mizma/ergoSHIFT/hardware-rev1/acrylic-shell/acryl-design-ergoSHIFT-Acrylic-layer-03.dxf

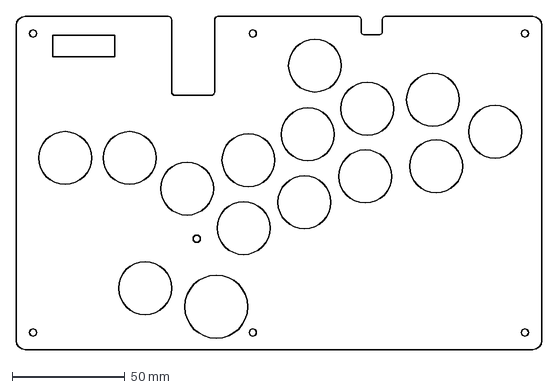
[picture p43: CAD file, 2023-12-16, an earlier design]
hardware-rev1/acrylic-shell/acryl-design-ergoSHIFT-Acrylic-layer-03.dxf
233.2 x 147.7 mm
