mizma/ergoSHIFT/ErgoSHIFT Layout/ErgoSHIFT_boardsize.pdf

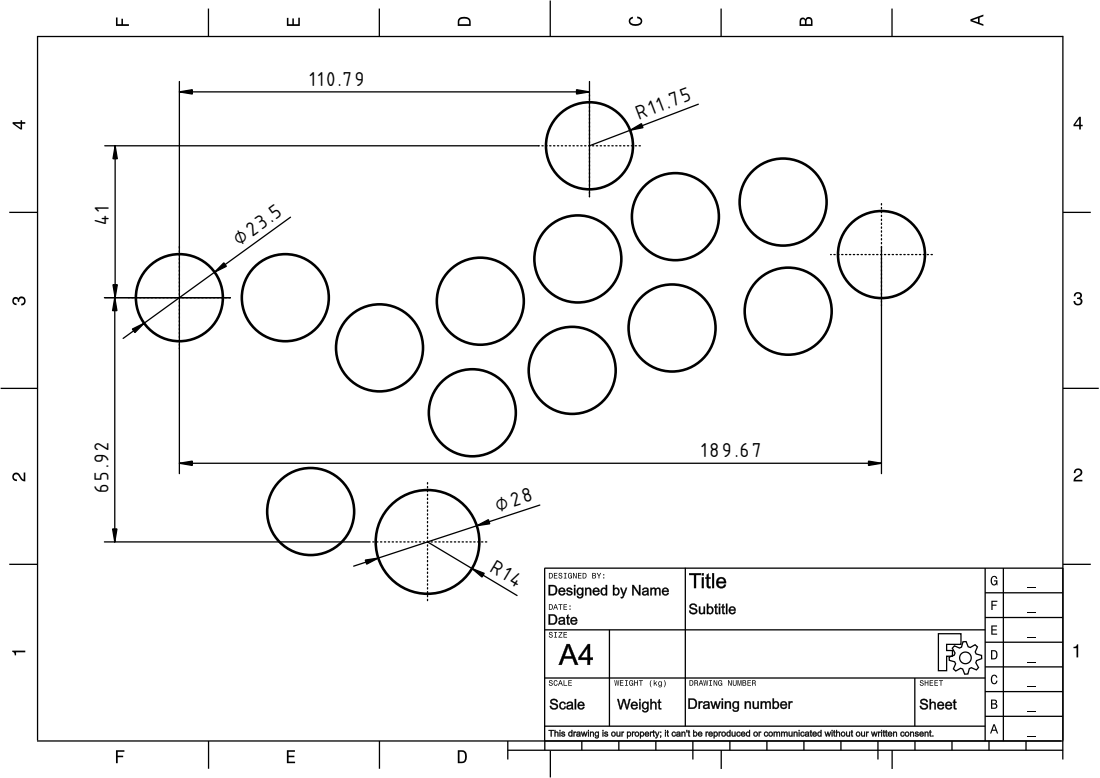
[picture p56: page 1]
