mizma/ergoSHIFT/hardware-rev1/acrylic-shell/acryl-design-ergoSHIFT-Acrylic-layer-02.pdf

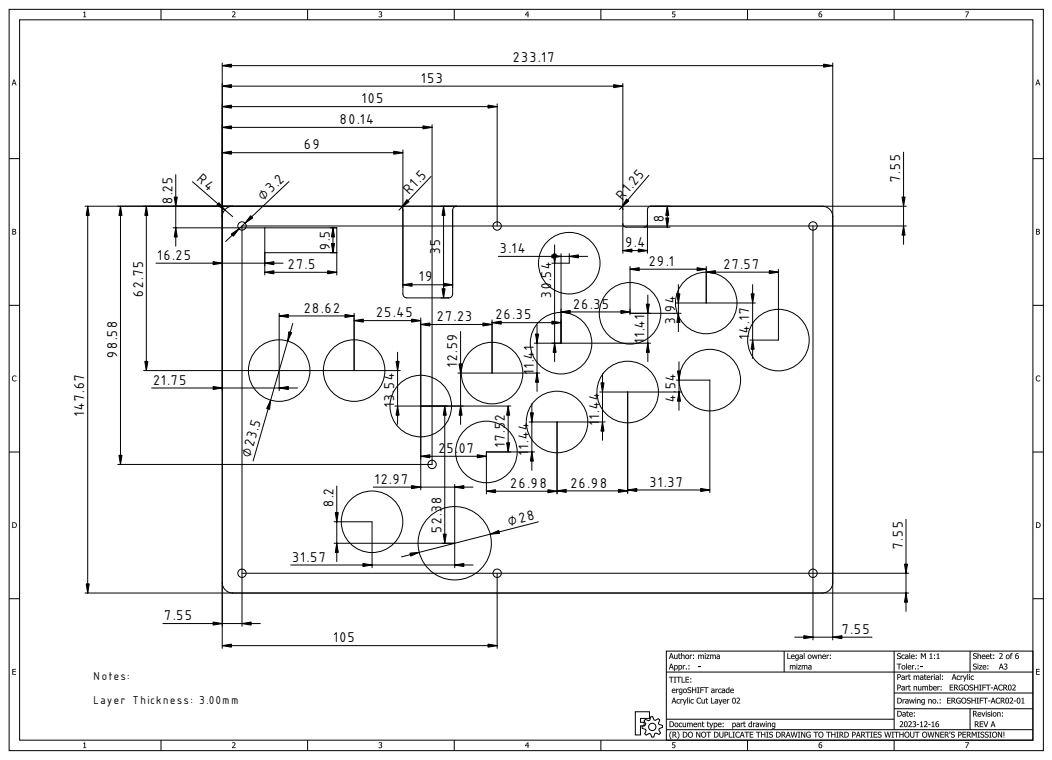
[picture p57: page 1]

7.55 7.55 233.17 147.67 ⌀ 28 ⌀ 23.5 9.5 27.5 19 359.4 8 R 1.25 R 1.5 ⌀ 3.2 R 4 98.58 80.14 7.55 7.55 21.75 28.62 25.45 12.97 25.07 27.23 26.35 3.14 26.35 29.1 27.57 31.57 26.98 26.98 31.37 13.54 12.59 17.52 11.4111.413.94 14.17 11.4411.444.54 52.388.2 69 153 105 105 30.5416.25 8.25 62.75 N otes: Layer T hickness: 3.00m m
