mizma/ergoSHIFT/hardware-rev1/acrylic-shell/pcb-design-ergoSHIFT-PCB-layer.pdf

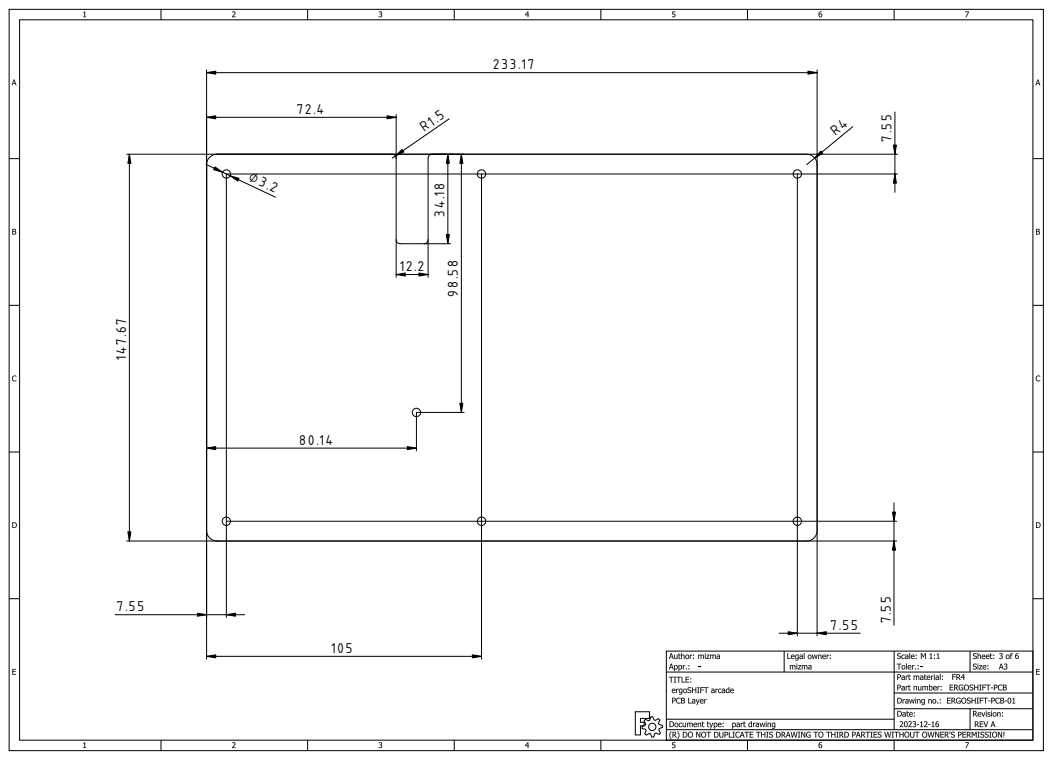
[picture p58: page 1]
