mizma/ergoSHIFT/hardware-rev1/design_data/ergoSHIFT-rev1-kicad/ergoSHIFT-Button-Layout.pdf

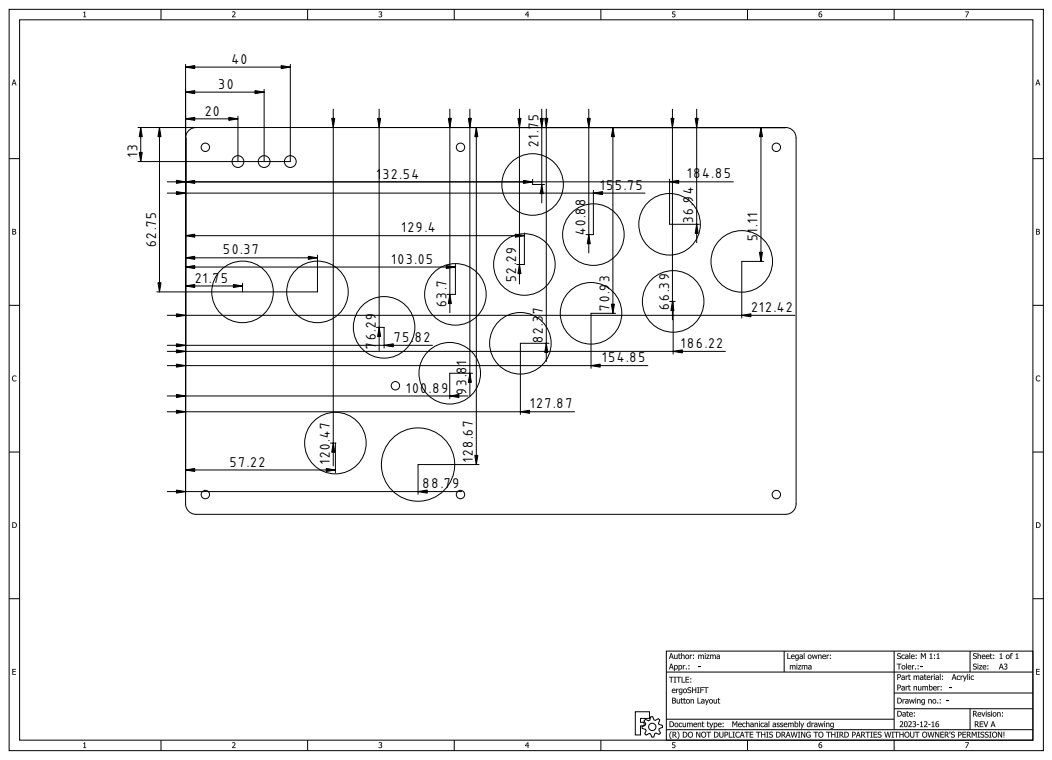
[picture p59: page 1]
